Supermagnum/FIS-Display/firmware/fis_nav_icons.h

#pragma once
/*
 * FIS nav/status icon bitmaps for the 3LB graphic display (64x64 px, 1-bit).
 *
 * Format: row-major; each row = 8 bytes (64 bits), MSB first (pixel 0 = bit 7 of byte 0).
 * Black = 1, white = 0. Total 512 bytes per icon.
 *
 * To add a new icon: add an SVG in nav-icons/, run
 *   python3 tools/svg_to_fis_icon.py nav-icons/your_icon.svg
 * then paste the generated array below, add its entry to FIS_ICON_TABLE (before the
 * sentinel {NULL, NULL, 0, 0}), and increment FIS_ICON_COUNT. See nav-icons/README.md.
 *
 * All-zero 512-byte icon: if an icon is exactly 512 bytes of zeros, the pixel data
 * was never written. Common causes:
 *   - Array declared but the fill/generation step did not run
 *   - Source SVG was not converted/exported properly (run svg_to_fis_icon.py again)
 *   - Data was zeroed during copy or flash
 *   - Wrong array referenced (actual data may be in a differently named variable)
 */
#include <stdint.h>

#ifdef __AVR__
#include <avr/pgmspace.h>
#else
#define PROGMEM
#endif

// nav_destination_bk.svg — 64x64px, 512 bytes
static const uint8_t ICON_NAV_DESTINATION_BK[] PROGMEM = {
  0x00, 0x00, 0x00, 0x00, 0x00, 0x00, 0x00, 0x00, 0x00, 0x00, 0x00, 0x00, 0x00, 0x00, 0x00, 0x00,
  0x00, 0x40, 0x00, 0x00, 0x00, 0x00, 0x00, 0x00, 0x00, 0xFF, 0x00, 0x00, 0x00, 0x00, 0x00, 0x00,
  0x00, 0xFF, 0xFC, 0x00, 0x00, 0x00, 0x00, 0x00, 0x00, 0xFF, 0xFF, 0xF0, 0x00, 0x00, 0x00, 0x00,
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
  0x00, 0x00, 0x00, 0x03, 0xC0, 0x00, 0x00, 0x00, 0x00, 0x00, 0x00, 0x01, 0x80, 0x00, 0x00, 0x00,
  0x00, 0x00, 0x00, 0x01, 0x80, 0x00, 0x00, 0x00, 0x00, 0x00, 0x00, 0x00, 0x00, 0x00, 0x00, 0x00,
};
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
